twasiluk/hdmilight/fpga/avr/prog_mem_content.vhd

library IEEE;
use IEEE.STD_LOGIC_1164.all;

package prog_mem_content is

-- content of p_0 ----------------------------------------------------------------------------------
constant p0_00 : BIT_VECTOR := X"C002E0E0E6A0BFCDE0D4BE1FC01BC01DC01FC021C023C025C027C029C02BC012";
constant p0_01 : BIT_VECTOR := X"0FE82FE201C0C007E0E081AA306393DFCFD1D1EE07B1921DE0B1E01107B1920D";
constant p0_02 : BIT_VECTOR := X"93DF950891DFE090C002E680E0F023229611539024110293E03A81BDF7B1912C";
constant p0_03 : BIT_VECTOR := X"B7CDE783B7FED000D000912CE0B02322963153A0241102A3E03A2DE080023062";
constant p0_04 : BIT_VECTOR := X"E04A2DE08002F00901FC91CFD20CE78ABF8DBF9EB60FB79ED513832483B3839A";
constant p0_05 : BIT_VECTOR := X"BF8DBF9EB60FB79EB548E08ABD87B568E0889530273323339631532024110224";
constant p0_06 : BIT_VECTOR := X"D1C0E982BF8DBF9EB60FB79ED4C78740835683648333938E9612B7ADE884B7FE";
constant p0_07 : BIT_VECTOR := X"C00924FF91FC961423229631531024110213E03A971391EDC0663064931F92FF";
constant p0_08 : BIT_VECTOR := X"D531D4DF23229631530024110203E03A971791EDF7A181200EF82EF924110243";
constant p0_09 : BIT_VECTOR := X"821582139711939CB7BEE0909631B7EDBE0F94F8970AB78DD529D52BD4D9D52F";
constant p0_0A : BIT_VECTOR := X"971391EDC0583064931F92FF90FF911FE090C003BE0F94F8960AB78D86118217";
constant p0_0B : BIT_VECTOR := X"F7B181200F082F0201C0C007E00091FC9614232296310EF2ED4001C02D4FE03A";
constant p0_0C : BIT_VECTOR := X"D0002F18E090D4B7D465D4BBD4BDD46B23229631531024110213E03A971791ED";
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
constant p1_32 : BIT_VECTOR := X"B58900000000BD89B5897F87C003E020950805919601E090BD89B58905919601";
constant p1_33 : BIT_VECTOR := X"9601E090BD89B5897F87CFDCF0115F2F00000000BD89B58905919601E090BD89";
constant p1_34 : BIT_VECTOR := X"0000E0807F8BE0209508F7E19587E0232F8905314F3F0000E0206084B7900591";
constant p1_35 : BIT_VECTOR := X"9F739F622F823038F7D9308A0000E08060842B28F7E19587E0430F22F7D9308A";
constant p1_36 : BIT_VECTOR := X"1BBB2E1A950801CF1FF90DB01FF90DB027999F659F749F839F920DE01DF19F82";
constant p1_37 : BIT_VECTOR := X"CFFF950801BD019B95809560941A1F881F660BE41BA207F507B31FFF1FBBC00D";
constant p1_38 : BIT_VECTOR := X"3D6474686C20726564252520203A007261207265642525006C617264203A6500";
constant p1_39 : BIT_VECTOR := X"612061767264203A650025206165326C203264616C6131726120726564252520";
constant p1_3A : BIT_VECTOR := X"FFFFFFFFFFFFFFFFFFFFFFFFFFFF464542413736333200200D000A0052563272";
constant p1_3B : BIT_VECTOR := X"FFFFFFFFFFFFFFFFFFFFFFFFFFFFFFFFFFFFFFFFFFFFFFFFFFFFFFFFFFFFFFFF";
constant p1_3C : BIT_VECTOR := X"FFFFFFFFFFFFFFFFFFFFFFFFFFFFFFFFFFFFFFFFFFFFFFFFFFFFFFFFFFFFFFFF";
constant p1_3D : BIT_VECTOR := X"FFFFFFFFFFFFFFFFFFFFFFFFFFFFFFFFFFFFFFFFFFFFFFFFFFFFFFFFFFFFFFFF";
constant p1_3E : BIT_VECTOR := X"FFFFFFFFFFFFFFFFFFFFFFFFFFFFFFFFFFFFFFFFFFFFFFFFFFFFFFFFFFFFFFFF";
constant p1_3F : BIT_VECTOR := X"FFFFFFFFFFFFFFFFFFFFFFFFFFFFFFFFFFFFFFFFFFFFFFFFFFFFFFFFFFFFFFFF";

end prog_mem_content;
